ZipCPU/openarty/doc/gfx/dbg.png

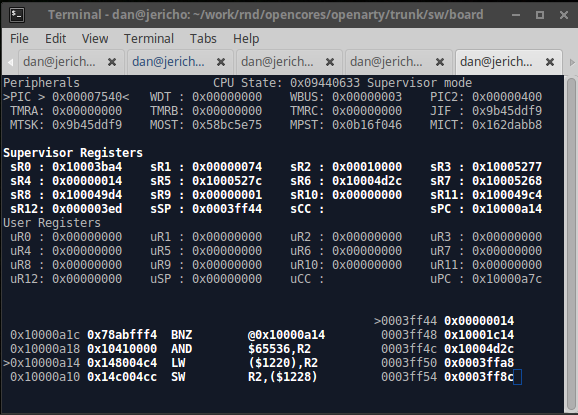
doc/gfx/dbg.png
