ZipCPU/openarty/doc/gfx/flashid.png

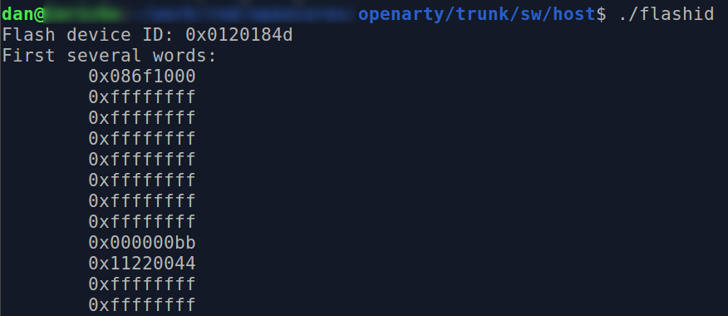
doc/gfx/flashid.png
