ZipCPU/openarty/doc/gfx/gps-traklog.png

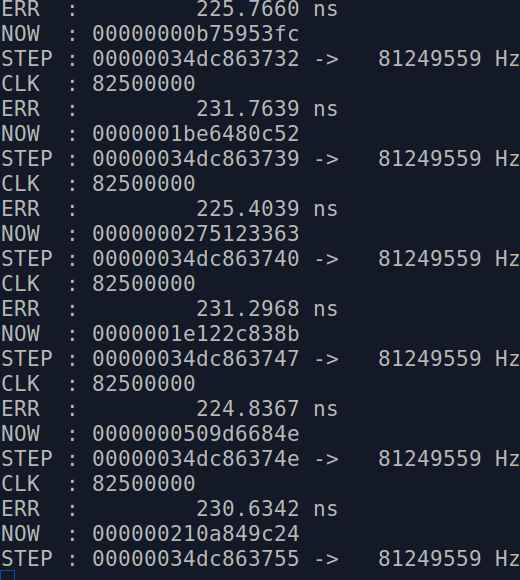
doc/gfx/gps-traklog.png
