ZipCPU/openarty/doc/gfx/mig_01-create.png

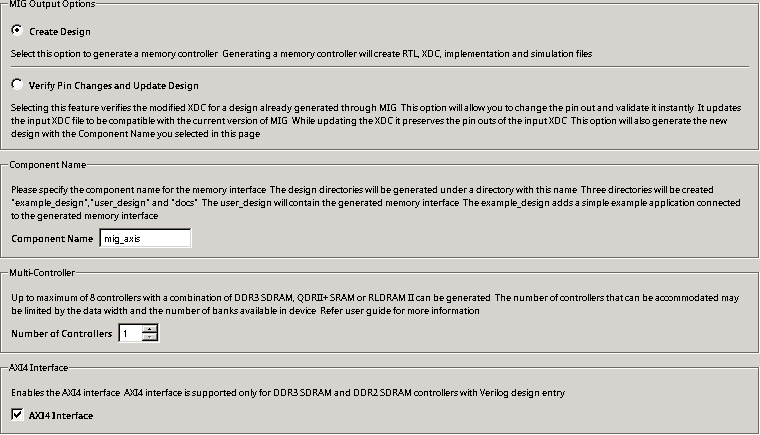
doc/gfx/mig_01-create.png
