ZipCPU/openarty/doc/gfx/mig_02-pincompat.png

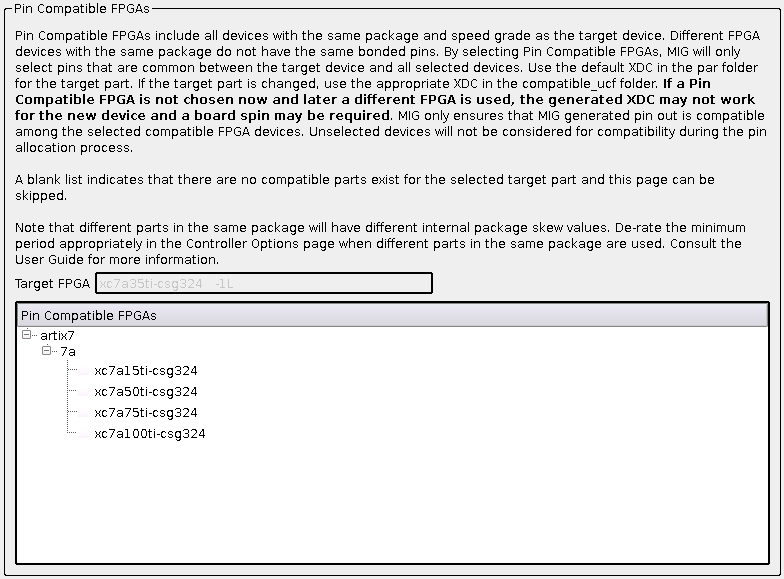
doc/gfx/mig_02-pincompat.png
