ZipCPU/openarty/doc/gfx/mig_08-fpgaopts.png

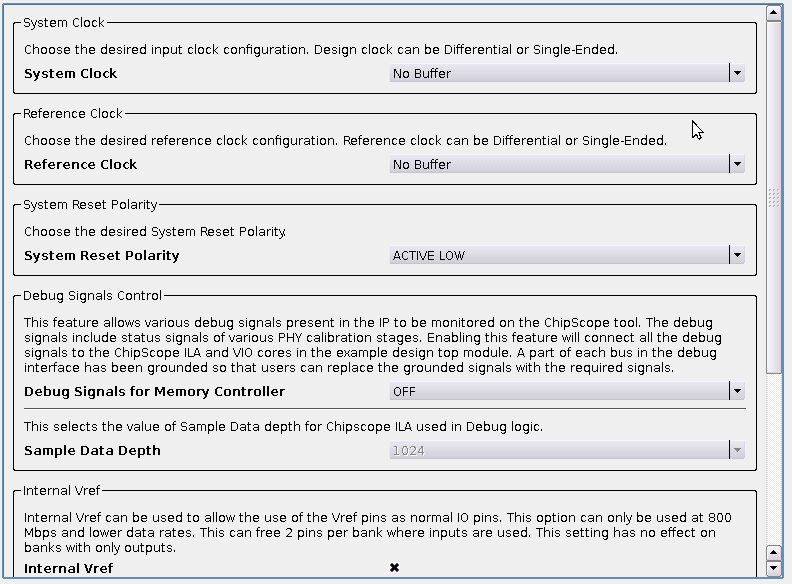
doc/gfx/mig_08-fpgaopts.png
