ZipCPU/openarty/doc/gfx/mig_13-validpins.png

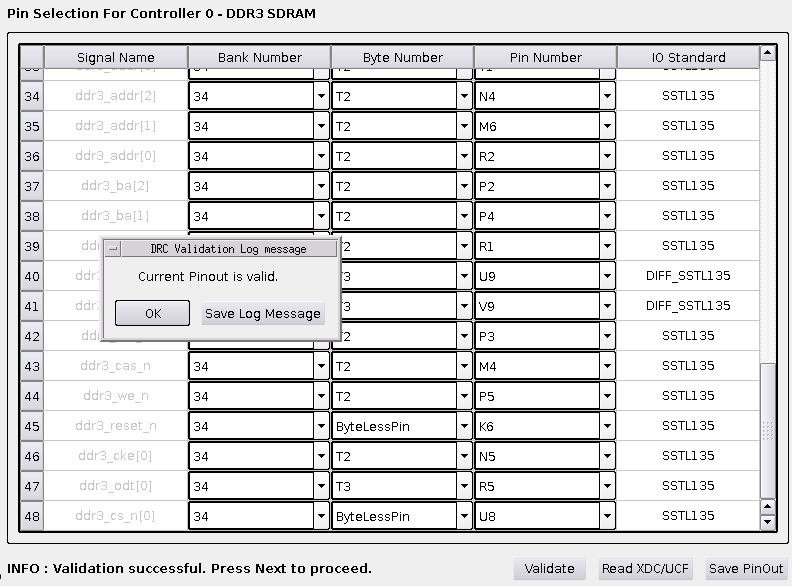
doc/gfx/mig_13-validpins.png
