ZipCPU/openarty/doc/gfx/ntpsrvr-box.png

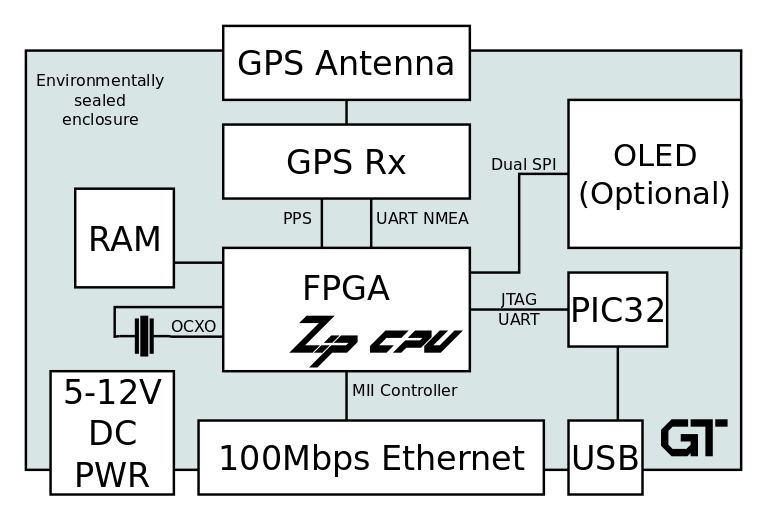
doc/gfx/ntpsrvr-box.png
