ZipCPU/openarty/doc/gfx/oledrgb-demo.png

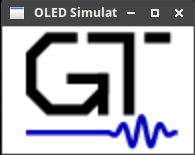
doc/gfx/oledrgb-demo.png
