ZipCPU/openarty/doc/gfx/openmig.png

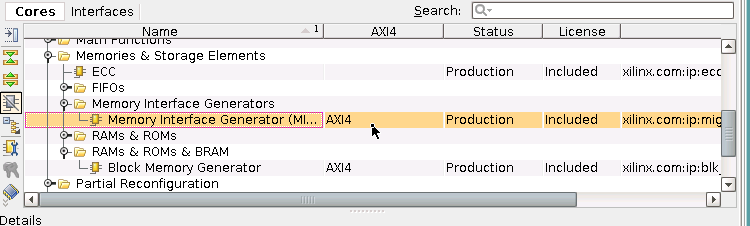
doc/gfx/openmig.png
