ZipCPU/openarty/doc/gfx/proj_dir.png

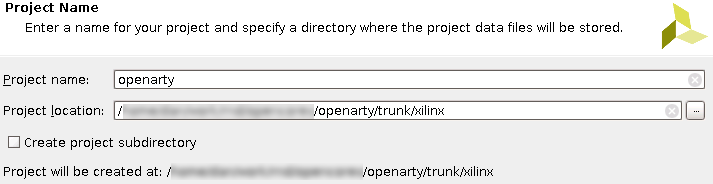
doc/gfx/proj_dir.png
