ZipCPU/openarty/scad/openarty.png

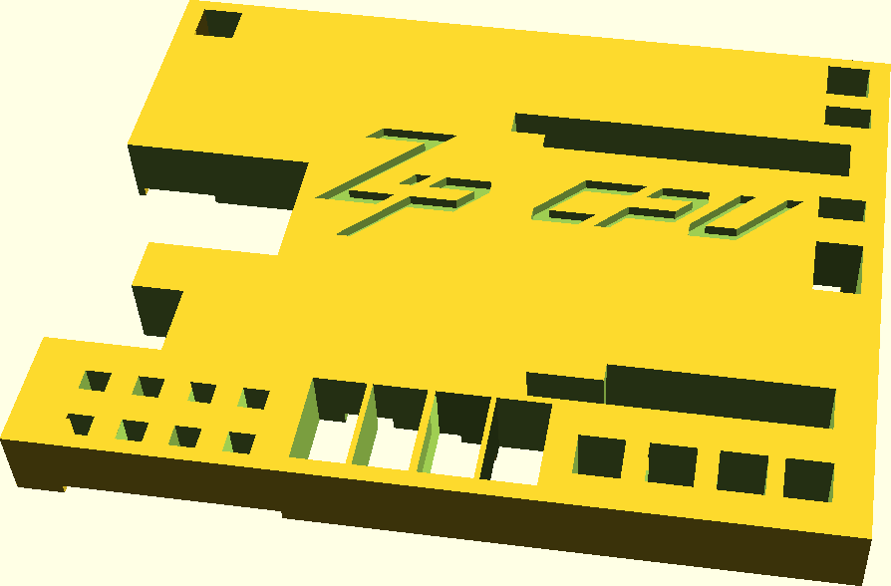
scad/openarty.png
