ZipCPU/openarty/doc/gfx/traking-costs.png

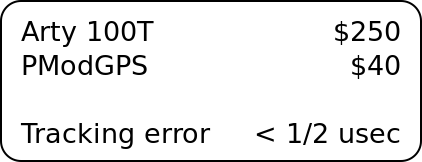
doc/gfx/traking-costs.png
