ZipCPU/openarty/rtl/wbm2axisp.v

////////////////////////////////////////////////////////////////////////////////
//
// Filename: 	wbm2axisp.v
//
// Project:	WB2AXIPSP: bus bridges and other odds and ends
//
// Purpose:	The B4 Wishbone SPEC allows transactions at a speed as fast as
//		one per clock.  The AXI bus allows transactions at a speed of
//	one read and one write transaction per clock.  These capabilities work
//	by allowing requests to take place prior to responses, such that the
//	requests might go out at once per clock and take several clocks, and
//	the responses may start coming back several clocks later.  In other
//	words, both protocols allow multiple transactions to be "in flight" at
//	the same time.  Current wishbone to AXI converters, however, handle only
//	one transaction at a time: initiating the transaction, and then waiting
//	for the transaction to complete before initiating the next.
//
//	The purpose of this core is to maintain the speed of both buses, while
//	transiting from the Wishbone (as master) to the AXI bus (as slave) and
//	back again.
//
// Creator:	Dan Gisselquist, Ph.D.
//		Gisselquist Technology, LLC
//
////////////////////////////////////////////////////////////////////////////////
//
// Copyright (C) 2016-2020, Gisselquist Technology, LLC
//
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
// This program is distributed in the hope that it will be useful, but WITHOUT
// ANY WARRANTY; without even the implied warranty of MERCHANTIBILITY or
// FITNESS FOR A PARTICULAR PURPOSE.  See the GNU General Public License
// for more details.
//
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
// License:	GPL, v3, as defined and found on www.gnu.org,
//		http://www.gnu.org/licenses/gpl.html
//
//
////////////////////////////////////////////////////////////////////////////////
//
//
`default_nettype	none
//
module wbm2axisp #(
	parameter C_AXI_DATA_WIDTH	= 128,// Width of the AXI R&W data
	parameter C_AXI_ADDR_WIDTH	=  28,	// AXI Address width (log wordsize)
	parameter C_AXI_ID_WIDTH	=   1,
	parameter DW			=  32,	// Wishbone data width
	parameter AW			=  26,	// Wishbone address width (log wordsize)
	parameter [C_AXI_ID_WIDTH-1:0] AXI_WRITE_ID = 1'b0,
	parameter [C_AXI_ID_WIDTH-1:0] AXI_READ_ID  = 1'b1,
	parameter LGFIFO		=   6
	) (
	input	wire			i_clk,	// System clock
	input	wire			i_reset,// Reset signal,drives AXI rst

	// AXI write address channel signals
	output	reg			o_axi_awvalid,	// Write address valid
	input	wire			i_axi_awready, // Slave is ready to accept
	output	wire	[C_AXI_ID_WIDTH-1:0]	o_axi_awid,	// Write ID
	output	reg	[C_AXI_ADDR_WIDTH-1:0]	o_axi_awaddr,	// Write address
	output	wire	[7:0]		o_axi_awlen,	// Write Burst Length
	output	wire	[2:0]		o_axi_awsize,	// Write Burst size
	output	wire	[1:0]		o_axi_awburst,	// Write Burst type
	output	wire	[0:0]		o_axi_awlock,	// Write lock type
	output	wire	[3:0]		o_axi_awcache,	// Write Cache type
	output	wire	[2:0]		o_axi_awprot,	// Write Protection type
	output	wire	[3:0]		o_axi_awqos,	// Write Quality of Svc

// AXI write data channel signals
	output	reg			o_axi_wvalid,	// Write valid
	input	wire			i_axi_wready,  // Write data ready
	output	reg	[C_AXI_DATA_WIDTH-1:0]	o_axi_wdata,	// Write data
	output	reg	[C_AXI_DATA_WIDTH/8-1:0] o_axi_wstrb,	// Write strobes
	output	wire			o_axi_wlast,	// Last write transaction

// AXI write response channel signals
	input	wire			i_axi_bvalid,  // Write reponse valid
	output	wire			o_axi_bready,  // Response ready
	input wire [C_AXI_ID_WIDTH-1:0]	i_axi_bid,	// Response ID
	input	wire [1:0]		i_axi_bresp,	// Write response

// AXI read address channel signals
	output	reg			o_axi_arvalid,	// Read address valid
	input	wire			i_axi_arready,	// Read address ready
	output	wire	[C_AXI_ID_WIDTH-1:0]	o_axi_arid,	// Read ID
	output	reg	[C_AXI_ADDR_WIDTH-1:0]	o_axi_araddr,	// Read address
	output	wire	[7:0]		o_axi_arlen,	// Read Burst Length
	output	wire	[2:0]		o_axi_arsize,	// Read Burst size
	output	wire	[1:0]		o_axi_arburst,	// Read Burst type
	output	wire	[0:0]		o_axi_arlock,	// Read lock type
	output	wire	[3:0]		o_axi_arcache,	// Read Cache type
	output	wire	[2:0]		o_axi_arprot,	// Read Protection type
	output	wire	[3:0]		o_axi_arqos,	// Read Protection type

// AXI read data channel signals
	input	wire			i_axi_rvalid,  // Read reponse valid
	output	wire			o_axi_rready,  // Read Response ready
	input wire [C_AXI_ID_WIDTH-1:0]	i_axi_rid,     // Response ID
	input wire [C_AXI_DATA_WIDTH-1:0] i_axi_rdata,    // Read data
	input	wire	[1:0]		i_axi_rresp,   // Read response
	input	wire			i_axi_rlast,    // Read last

	// We'll share the clock and the reset
	input	wire			i_wb_cyc,
	input	wire			i_wb_stb,
	input	wire			i_wb_we,
	input	wire	[(AW-1):0]	i_wb_addr,
	input	wire	[(DW-1):0]	i_wb_data,
	input	wire	[(DW/8-1):0]	i_wb_sel,
	output	reg			o_wb_stall,
	output	reg			o_wb_ack,
	output	reg	[(DW-1):0]	o_wb_data,
	output	reg			o_wb_err
);

//*****************************************************************************
// Parameter declarations
//*****************************************************************************

	localparam	LG_AXI_DW	= $clog2(C_AXI_DATA_WIDTH);
	localparam	LG_WB_DW	= $clog2(DW);
	localparam	FIFOLN = (1<<LGFIFO);
	localparam	SUBW = LG_AXI_DW-LG_WB_DW;

	// The various address widths must be properly related.  We'll insist
	// upon that relationship here.
	initial begin
		if (C_AXI_DATA_WIDTH < DW)
			$stop;
		if (C_AXI_ADDR_WIDTH != AW + $clog2(DW)-3)
			$stop;
		if (	  (C_AXI_DATA_WIDTH / DW !=32)
			&&(C_AXI_DATA_WIDTH / DW !=16)
			&&(C_AXI_DATA_WIDTH / DW != 8)
			&&(C_AXI_DATA_WIDTH / DW != 4)
			&&(C_AXI_DATA_WIDTH / DW != 2)
			&&(C_AXI_DATA_WIDTH      != DW))
			$stop;
	end

//*****************************************************************************
// Internal register and wire declarations
//*****************************************************************************

// Things we're not changing ...
	localparam	DWSIZE = $clog2(DW)-3;
	assign o_axi_awid    = AXI_WRITE_ID;
	assign o_axi_awlen   = 8'h0;	// Burst length is one
	assign o_axi_awsize  = DWSIZE[2:0];
	assign o_axi_wlast   = 1;
	assign o_axi_awburst = 2'b01;	// Incrementing address (ignored)
	assign o_axi_awlock  = 1'b0;	// Normal signaling
	assign o_axi_arlock  = 1'b0;	// Normal signaling
	assign o_axi_awcache = 4'h3;	// Normal: no cache, modifyable
	//
	assign o_axi_arid    = AXI_READ_ID;
	assign o_axi_arlen   = 8'h0;	// Burst length is one
	assign o_axi_arsize  = DWSIZE[2:0];
	assign o_axi_arburst = 2'b01;	// Incrementing address (ignored)
	assign o_axi_arcache = 4'h3;	// Normal: no cache, modifyable
	assign o_axi_awprot  = 3'b010;	// Unpriviledged, unsecure, data access
	assign o_axi_arprot  = 3'b010;	// Unpriviledged, unsecure, data access
	assign o_axi_awqos   = 4'h0;	// Lowest quality of service (unused)
	assign o_axi_arqos   = 4'h0;	// Lowest quality of service (unused)

	wire	[$clog2(DW)-4:0]	axi_lsbs;
	assign	axi_lsbs = 0;

	reg			direction, full, empty, flushing, nearfull;
	reg	[LGFIFO:0]	npending;
	//
	wire			skid_ready, m_valid, m_we;
	reg			m_ready;
	wire	[AW-1:0]	m_addr;
	wire	[DW-1:0]	m_data;
	wire	[DW/8-1:0]	m_sel;

// Command logic
	initial	direction = 0;
	always @(posedge i_clk)
	if (empty)
		direction <= m_we;

	initial	npending = 0;
	initial	empty    = 1;
	initial	full     = 0;
	initial	nearfull = 0;
	always @(posedge i_clk)
	if (i_reset)
	begin
		npending <= 0;
		empty    <= 1;
		full     <= 0;
		nearfull <= 0;
	end else case ({m_valid && m_ready, i_axi_bvalid||i_axi_rvalid})
	2'b10: begin
		npending <= npending + 1;
		empty <= 0;
		nearfull <= &(npending[LGFIFO-1:1]);
		full <= &(npending[LGFIFO-1:0]);
		end
	2'b01: begin
		nearfull <= full;
		npending <= npending - 1;
		empty <= (npending == 1);
		full <= 0;
		end
	default: begin end
	endcase

	initial	flushing = 0;
	always @(posedge i_clk)
	if (i_reset)
		flushing <= 0;
	else if ((i_axi_rvalid && i_axi_rresp[1])
		||(i_axi_bvalid && i_axi_bresp[1])
		||(!i_wb_cyc && !empty))
		flushing <= 1'b1;
	else if (empty)
		flushing <= 1'b0;

	////////////////////////////////////////////////////////////////////////
	//
	// Wishbone input skidbuffer
	//
	////////////////////////////////////////////////////////////////////////
	//
	//
	skidbuffer #(.DW(1+AW+DW+(DW/8)),
		.OPT_OUTREG(1'b0))
	skid (i_clk, i_reset || !i_wb_cyc,
		i_wb_stb, skid_ready,
			{ i_wb_we, i_wb_addr, i_wb_data, i_wb_sel },
		m_valid, m_ready,
			{ m_we, m_addr, m_data, m_sel });

	always @(*)
		o_wb_stall = !skid_ready;

	always @(*)
	begin
		m_ready = 1;

		if (flushing || nearfull || ((m_we != direction)&&(!empty)))
			m_ready = 1'b0;
		if (o_axi_awvalid && !i_axi_awready)
			m_ready = 1'b0;
		if (o_axi_wvalid && !i_axi_wready)
			m_ready = 1'b0;
		if (o_axi_arvalid && !i_axi_arready)
			m_ready = 1'b0;
	end

	////////////////////////////////////////////////////////////////////////
	//
	// AXI Signaling
	//
	////////////////////////////////////////////////////////////////////////
	//
	//

	// Send write transactions
	initial	o_axi_awvalid = 0;
	initial	o_axi_wvalid = 0;
	always @(posedge i_clk)
	if (i_reset)
	begin
		o_axi_awvalid <= 0;
		o_axi_wvalid  <= 0;
	end else if (m_valid && m_we && m_ready)
	begin
		o_axi_awvalid <= 1;
		o_axi_wvalid  <= 1;
	end else begin
		if (i_axi_awready)
			o_axi_awvalid <= 0;
		if (i_axi_wready)
			o_axi_wvalid <= 0;
	end

	always @(posedge i_clk)
	if (!o_axi_wvalid || i_axi_wready)
		o_axi_wdata   <= {(C_AXI_DATA_WIDTH/DW){m_data}};

	// Send read transactions
	initial	o_axi_arvalid = 0;
	always @(posedge i_clk)
	if (i_reset)
		o_axi_arvalid <= 0;
	else if (m_valid && !m_we && m_ready)
		o_axi_arvalid <= 1;
	else if (i_axi_arready)
	begin
		o_axi_arvalid <= 0;
	end

	generate if (DW == 8)
	begin

		always @(posedge i_clk)
		if (!o_axi_awvalid || i_axi_awready)
			o_axi_awaddr  <= m_addr;

		always @(posedge i_clk)
		if (!o_axi_arvalid || i_axi_arready)
			o_axi_araddr  <= m_addr;

	end else begin
		always @(posedge i_clk)
		if (!o_axi_awvalid || i_axi_awready)
			o_axi_awaddr  <= { m_addr, axi_lsbs };

		always @(posedge i_clk)
		if (!o_axi_arvalid || i_axi_arready)
			o_axi_araddr  <= { m_addr, axi_lsbs };

	end endgenerate


	generate if (DW == C_AXI_DATA_WIDTH)
	begin

		always @(posedge i_clk)
		if (!o_axi_wvalid || i_axi_wready)
			o_axi_wstrb   <= m_sel;

	end else if (DW*2 == C_AXI_DATA_WIDTH)
	// {{{
	begin

		always @(posedge i_clk)
		if (!o_axi_wvalid || i_axi_wready)
		begin
			if (m_addr[0])
				o_axi_wstrb   <= { m_sel, {(DW/8){1'b0}} };
			else
				o_axi_wstrb   <= { {(DW/8){1'b0}}, m_sel };
		end

	end else if (DW*4 == C_AXI_DATA_WIDTH)
	begin

		always @(posedge i_clk)
		if (!o_axi_wvalid || i_axi_wready) case(~m_addr[1:0])
		2'b00: o_axi_wstrb   <= { m_sel, {(3*DW/8){1'b0}} };
		2'b01: o_axi_wstrb   <= { {(  DW/8){1'b0}}, m_sel, {(2*DW/8){1'b0}} };
		2'b10: o_axi_wstrb   <= { {(2*DW/8){1'b0}}, m_sel, {(  DW/8){1'b0}} };
		2'b11: o_axi_wstrb   <= { {(3*DW/8){1'b0}}, m_sel };
		endcase

	end else if (DW*8 == C_AXI_DATA_WIDTH)
	begin

		always @(posedge i_clk)
		if (!o_axi_wvalid || i_axi_wready) case(~m_addr[2:0])
		3'b000: o_axi_wstrb   <= { m_sel, {(7*DW/8){1'b0}} };
		3'b001: o_axi_wstrb   <= { {(  DW/8){1'b0}}, m_sel, {(6*DW/8){1'b0}} };
		3'b010: o_axi_wstrb   <= { {(2*DW/8){1'b0}}, m_sel, {(5*DW/8){1'b0}} };
		3'b011: o_axi_wstrb   <= { {(3*DW/8){1'b0}}, m_sel, {(4*DW/8){1'b0}} };
		3'b100: o_axi_wstrb   <= { {(4*DW/8){1'b0}}, m_sel, {(3*DW/8){1'b0}} };
		3'b101: o_axi_wstrb   <= { {(5*DW/8){1'b0}}, m_sel, {(2*DW/8){1'b0}} };
		3'b110: o_axi_wstrb   <= { {(6*DW/8){1'b0}}, m_sel, {(  DW/8){1'b0}} };
		3'b111: o_axi_wstrb   <= { {(7*DW/8){1'b0}}, m_sel };
		endcase

	end else if (DW*16 == C_AXI_DATA_WIDTH)
	begin

		always @(posedge i_clk)
		if (!o_axi_wvalid || i_axi_wready) case(~m_addr[3:0])
		4'b0000: o_axi_wstrb   <= { m_sel, {(15*DW/8){1'b0}} };
		4'b0001: o_axi_wstrb   <= { {(   DW/8){1'b0}}, m_sel, {(14*DW/8){1'b0}} };
		4'b0010: o_axi_wstrb   <= { {( 2*DW/8){1'b0}}, m_sel, {(13*DW/8){1'b0}} };
		4'b0011: o_axi_wstrb   <= { {( 3*DW/8){1'b0}}, m_sel, {(12*DW/8){1'b0}} };
		4'b0100: o_axi_wstrb   <= { {( 4*DW/8){1'b0}}, m_sel, {(11*DW/8){1'b0}} };
		4'b0101: o_axi_wstrb   <= { {( 5*DW/8){1'b0}}, m_sel, {(10*DW/8){1'b0}} };
		4'b0110: o_axi_wstrb   <= { {( 6*DW/8){1'b0}}, m_sel, {( 9*DW/8){1'b0}} };
		4'b0111: o_axi_wstrb   <= { {( 7*DW/8){1'b0}}, m_sel, {( 8*DW/8){1'b0}} };
		4'b1000: o_axi_wstrb   <= { {( 8*DW/8){1'b0}}, m_sel, {( 7*DW/8){1'b0}} };
		4'b1001: o_axi_wstrb   <= { {( 9*DW/8){1'b0}}, m_sel, {( 6*DW/8){1'b0}} };
		4'b1010: o_axi_wstrb   <= { {(10*DW/8){1'b0}}, m_sel, {( 5*DW/8){1'b0}} };
		4'b1011: o_axi_wstrb   <= { {(11*DW/8){1'b0}}, m_sel, {( 4*DW/8){1'b0}} };
		4'b1100: o_axi_wstrb   <= { {(12*DW/8){1'b0}}, m_sel, {( 3*DW/8){1'b0}} };
		4'b1101: o_axi_wstrb   <= { {(13*DW/8){1'b0}}, m_sel, {( 2*DW/8){1'b0}} };
		4'b1110: o_axi_wstrb   <= { {(14*DW/8){1'b0}}, m_sel, {(   DW/8){1'b0}} };
		4'b1111: o_axi_wstrb   <= { {(15*DW/8){1'b0}}, m_sel };
		endcase

	end else if (DW*32 == C_AXI_DATA_WIDTH)
	begin

		always @(posedge i_clk)
		if (!o_axi_wvalid || i_axi_wready) case(~m_addr[4:0])
		5'b00000: o_axi_wstrb   <= { m_sel, {(31*DW/8){1'b0}} };
		5'b00001: o_axi_wstrb   <= { {(   DW/8){1'b0}}, m_sel, {(30*DW/8){1'b0}} };
		5'b00010: o_axi_wstrb   <= { {( 2*DW/8){1'b0}}, m_sel, {(29*DW/8){1'b0}} };
		5'b00011: o_axi_wstrb   <= { {( 3*DW/8){1'b0}}, m_sel, {(28*DW/8){1'b0}} };
		5'b00100: o_axi_wstrb   <= { {( 4*DW/8){1'b0}}, m_sel, {(27*DW/8){1'b0}} };
		5'b00101: o_axi_wstrb   <= { {( 5*DW/8){1'b0}}, m_sel, {(26*DW/8){1'b0}} };
		5'b00110: o_axi_wstrb   <= { {( 6*DW/8){1'b0}}, m_sel, {(25*DW/8){1'b0}} };
		5'b00111: o_axi_wstrb   <= { {( 7*DW/8){1'b0}}, m_sel, {(24*DW/8){1'b0}} };
		5'b01000: o_axi_wstrb   <= { {( 8*DW/8){1'b0}}, m_sel, {(23*DW/8){1'b0}} };
		5'b01001: o_axi_wstrb   <= { {( 9*DW/8){1'b0}}, m_sel, {(22*DW/8){1'b0}} };
		5'b01010: o_axi_wstrb   <= { {(10*DW/8){1'b0}}, m_sel, {(21*DW/8){1'b0}} };
		5'b01011: o_axi_wstrb   <= { {(11*DW/8){1'b0}}, m_sel, {(20*DW/8){1'b0}} };
		5'b01100: o_axi_wstrb   <= { {(12*DW/8){1'b0}}, m_sel, {(19*DW/8){1'b0}} };
		5'b01101: o_axi_wstrb   <= { {(13*DW/8){1'b0}}, m_sel, {(18*DW/8){1'b0}} };
		5'b01110: o_axi_wstrb   <= { {(14*DW/8){1'b0}}, m_sel, {(17*DW/8){1'b0}} };
		5'b01111: o_axi_wstrb   <= { {(15*DW/8){1'b0}}, m_sel, {(16*DW/8){1'b0}} };
		5'b10000: o_axi_wstrb   <= { {(16*DW/8){1'b0}}, m_sel, {(15*DW/8){1'b0}} };
		5'b10001: o_axi_wstrb   <= { {(17*DW/8){1'b0}}, m_sel, {(14*DW/8){1'b0}} };
		5'b10010: o_axi_wstrb   <= { {(18*DW/8){1'b0}}, m_sel, {(13*DW/8){1'b0}} };
		5'b10011: o_axi_wstrb   <= { {(19*DW/8){1'b0}}, m_sel, {(12*DW/8){1'b0}} };
		5'b10100: o_axi_wstrb   <= { {(20*DW/8){1'b0}}, m_sel, {(11*DW/8){1'b0}} };
		5'b10101: o_axi_wstrb   <= { {(21*DW/8){1'b0}}, m_sel, {(10*DW/8){1'b0}} };
		5'b10110: o_axi_wstrb   <= { {(22*DW/8){1'b0}}, m_sel, {( 9*DW/8){1'b0}} };
		5'b10111: o_axi_wstrb   <= { {(23*DW/8){1'b0}}, m_sel, {( 8*DW/8){1'b0}} };
		5'b11000: o_axi_wstrb   <= { {(24*DW/8){1'b0}}, m_sel, {( 7*DW/8){1'b0}} };
		5'b11001: o_axi_wstrb   <= { {(25*DW/8){1'b0}}, m_sel, {( 6*DW/8){1'b0}} };
		5'b11010: o_axi_wstrb   <= { {(26*DW/8){1'b0}}, m_sel, {( 5*DW/8){1'b0}} };
		5'b11011: o_axi_wstrb   <= { {(27*DW/8){1'b0}}, m_sel, {( 4*DW/8){1'b0}} };
		5'b11100: o_axi_wstrb   <= { {(28*DW/8){1'b0}}, m_sel, {( 3*DW/8){1'b0}} };
		5'b11101: o_axi_wstrb   <= { {(29*DW/8){1'b0}}, m_sel, {( 2*DW/8){1'b0}} };
		5'b11110: o_axi_wstrb   <= { {(30*DW/8){1'b0}}, m_sel, {(   DW/8){1'b0}} };
		5'b11111: o_axi_wstrb   <= { {(31*DW/8){1'b0}}, m_sel };
		endcase
	// }}}
	end endgenerate

	generate if (DW == C_AXI_DATA_WIDTH)
	begin : NO_READ_DATA_SELECT_NECESSARY

		always @(*)
			o_wb_data = i_axi_rdata;

		always @(*)
			o_wb_ack = !flushing&&((i_axi_rvalid && !i_axi_rresp[1])
				||(i_axi_bvalid && !i_axi_bresp[1]));

		always @(*)
			o_wb_err = !flushing&&((i_axi_rvalid && i_axi_rresp[1])
				||(i_axi_bvalid && i_axi_bresp[1]));

	end else begin : READ_FIFO_DATA_SELECT
	// {{{

		reg	[SUBW-1:0]	addr_fifo	[0:(1<<LGFIFO)-1];
		reg	[SUBW-1:0]	fifo_value;
		reg	[LGFIFO:0]	wr_addr, rd_addr;
		wire	[C_AXI_DATA_WIDTH-1:0]	return_data;

		initial	o_wb_ack = 0;
		always @(posedge i_clk)
		if (i_reset || !i_wb_cyc || flushing)
			o_wb_ack <= 0;
		else
			o_wb_ack <= ((i_axi_rvalid && !i_axi_rresp[1])
				||(i_axi_bvalid && !i_axi_bresp[1]));

		initial	o_wb_err = 0;
		always @(posedge i_clk)
		if (i_reset || !i_wb_cyc || flushing)
			o_wb_err <= 0;
		else
			o_wb_err <= ((i_axi_rvalid && i_axi_rresp[1])
				||(i_axi_bvalid && i_axi_bresp[1]));


		initial	wr_addr = 0;
		always @(posedge i_clk)
		if (i_reset)
			wr_addr <= 0;
		else if (m_valid && m_ready)
			wr_addr <= wr_addr + 1;

		always @(posedge i_clk)
		if (m_valid && m_ready)
			addr_fifo[wr_addr[LGFIFO-1:0]] <= i_wb_addr[SUBW-1:0];

		initial	rd_addr = 0;
		always @(posedge i_clk)
		if (i_reset)
			rd_addr <= 0;
		else if (i_axi_bvalid || i_axi_rvalid)
			rd_addr <= rd_addr + 1;

		always @(*)
			fifo_value = addr_fifo[rd_addr[LGFIFO-1:0]];

		assign	return_data = i_axi_rdata >> (fifo_value * DW);

		always @(posedge i_clk)
			o_wb_data <= return_data[DW-1:0];

		// Make Verilator happy here
		if (C_AXI_DATA_WIDTH > DW)
		begin : UNUSED_DATA
			// verilator lint_off UNUSED
			wire	unused_data;
			assign	unused_data = &{ 1'b0,
					return_data[C_AXI_DATA_WIDTH-1:DW] };
		end
		// verilator lint_on  UNUSED
`ifdef	FORMAL
		always @(*)
			assert(wr_addr - rd_addr == npending);

		always @(*)
			assert(empty == (wr_addr == rd_addr));


		//
		// ...
		//
`endif
	// }}}
	end endgenerate

	// Read data channel / response logic
	assign	o_axi_rready = 1'b1;
	assign	o_axi_bready = 1'b1;

	// Make verilator's -Wall happy
	// verilator lint_off UNUSED
	wire	unused;
	assign	unused = &{ 1'b0, full, i_axi_bid, i_axi_bresp[0], i_axi_rid, i_axi_rresp[0], i_axi_rlast, m_data, m_sel };
	generate if (C_AXI_DATA_WIDTH > DW)
	begin
		wire	[C_AXI_DATA_WIDTH-1:DW] unused_data;
		assign	unused_data = i_axi_rdata[C_AXI_DATA_WIDTH-1:DW];
	end endgenerate
	// verilator lint_on  UNUSED
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
